Sylensky/OG-star-tracker-/community_upgrades/surveyor_tripod_adapter/size-test.stl

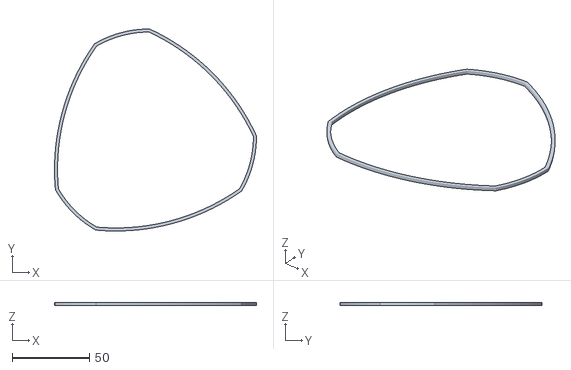
[picture p23: CAD file, 2025-09-13]
community_upgrades/surveyor_tripod_adapter/size-test.stl
130.6 x 130.6 x 2.00
