Sylensky/OG-star-tracker-/mechanics/Heavy duty/arcs-for-hd.stl

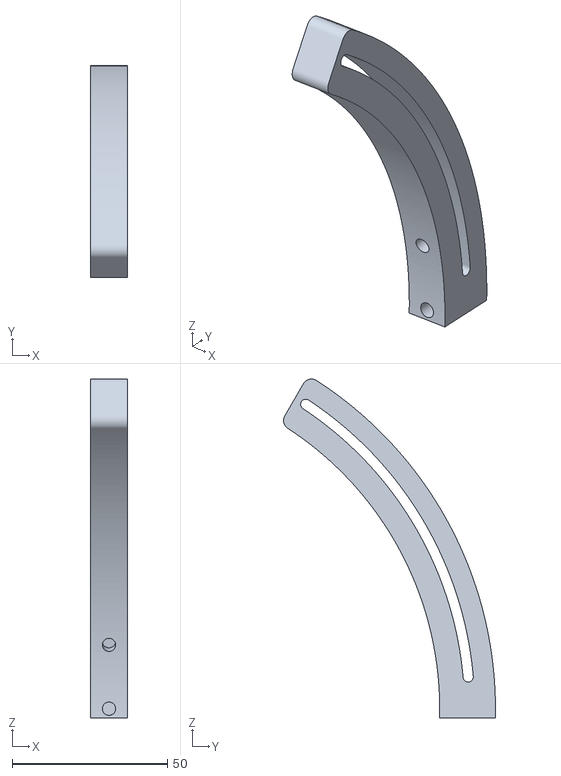
[picture p24: CAD file, 2025-09-13]
mechanics/Heavy duty/arcs-for-hd.stl
12.0 x 68.4 x 109.4
