Sylensky/OG-star-tracker-/mechanics/Manual go-to beta testing/vixen-knob.stl

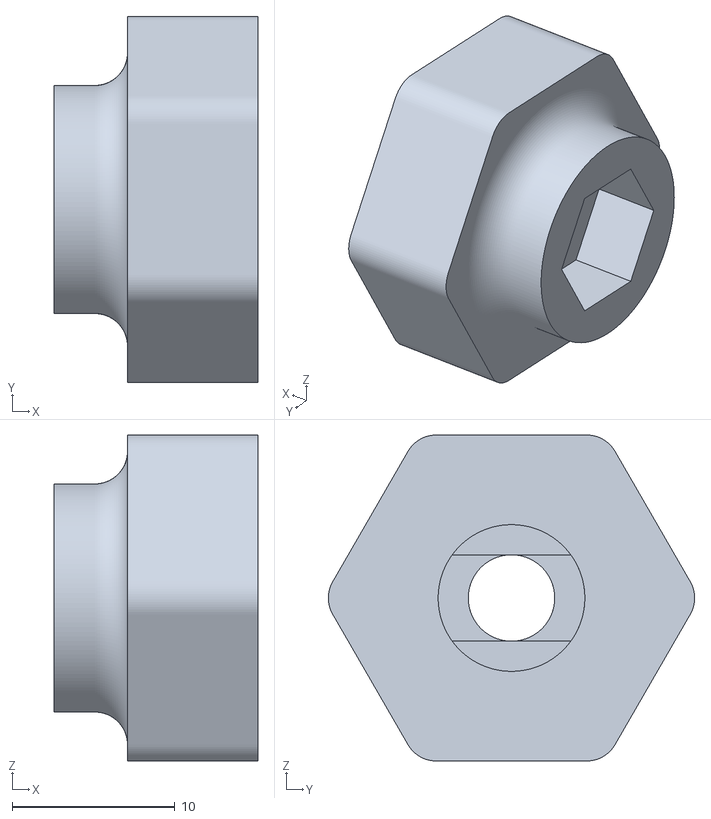
[picture p25: CAD file, 2025-09-13]
mechanics/Manual go-to beta testing/vixen-knob.stl
12.5 x 22.5 x 20.0
