Sylensky/OG-star-tracker-/mechanics/V2 files/polar-knob.stl

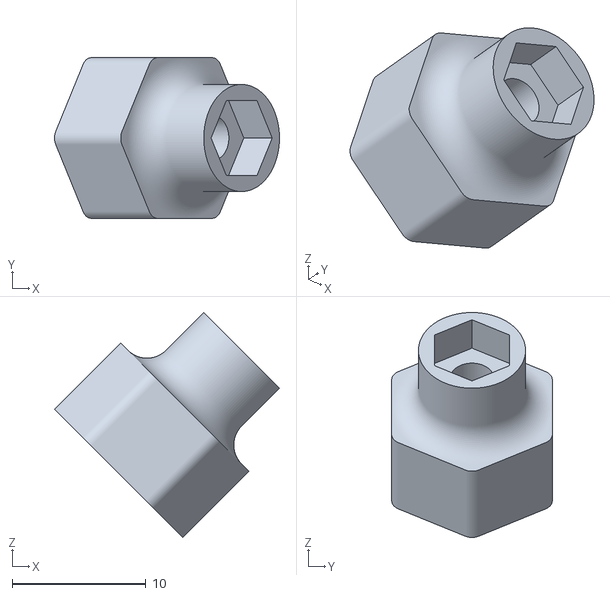
[picture p26: CAD file, 2025-09-13]
mechanics/V2 files/polar-knob.stl
16.8 x 12.0 x 16.8
