Sylensky/OG-star-tracker-/community_upgrades/beefier_gearbox_multicolor/stls/belt-tightener-f695-bearing-m5x16mm.stl

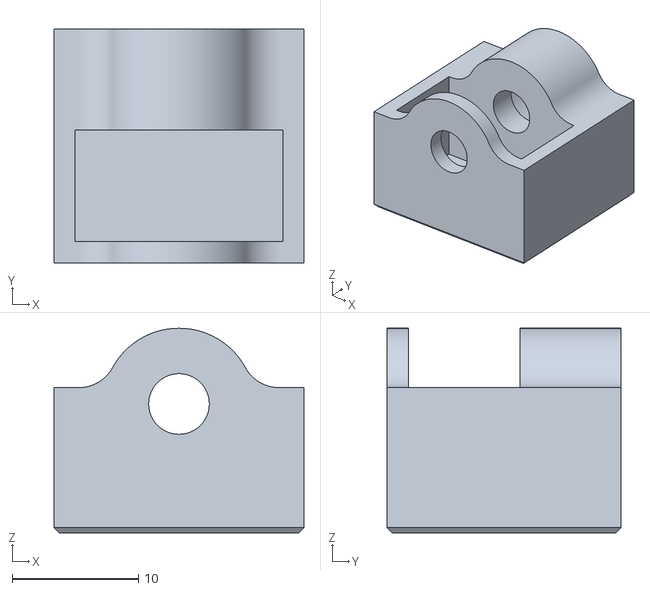
[picture p27: CAD file, 2025-09-13]
community_upgrades/beefier_gearbox_multicolor/stls/belt-tightener-f695-bearing-m5x16mm.stl
19.8 x 18.5 x 16.2
