Sylensky/OG-star-tracker-/community_upgrades/illuminated_polarscope/stls/scope-mount-body-pot-and-switch-v11.stl

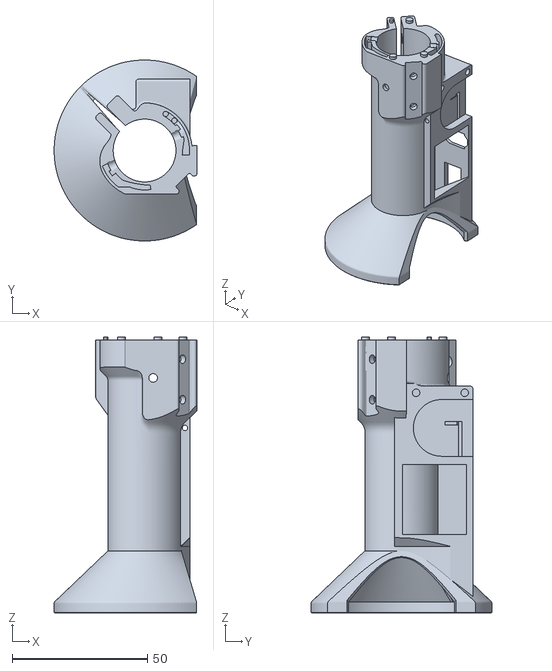
[picture p28: CAD file, 2025-10-03]
community_upgrades/illuminated_polarscope/stls/scope-mount-body-pot-and-switch-v11.stl
52.9 x 67.0 x 102.2
