Sylensky/OG-star-tracker-/mechanics/Manual go-to beta testing/big-scale.stl

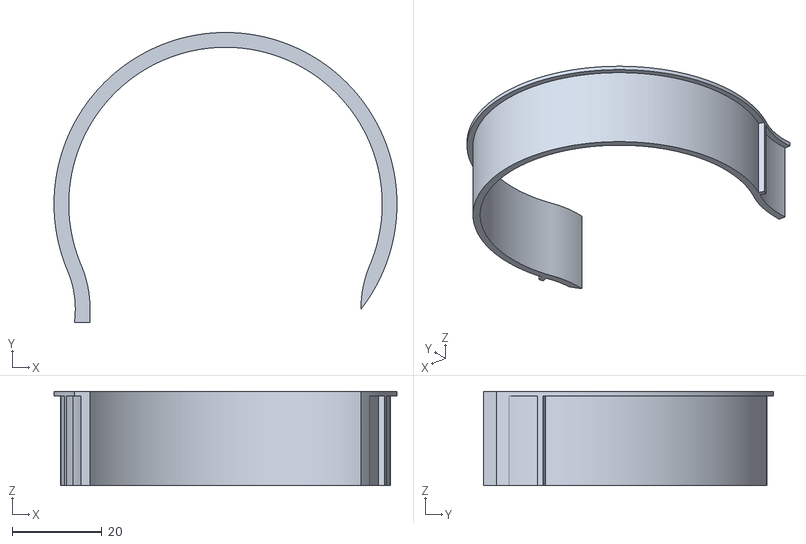
[picture p29: CAD file, 2025-09-13]
mechanics/Manual go-to beta testing/big-scale.stl
76.5 x 64.7 x 21.0
