Sylensky/OG-star-tracker-/mechanics/V2 files/bottom-bearing-holder.stl

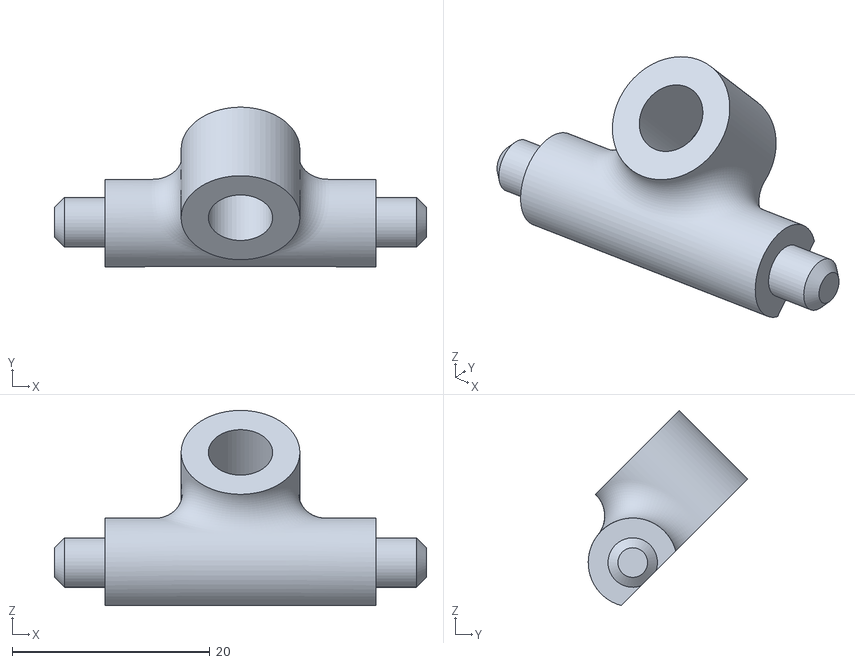
[picture p30: CAD file, 2025-09-13]
mechanics/V2 files/bottom-bearing-holder.stl
37.6 x 16.1 x 19.7
