Sylensky/OG-star-tracker-/community_upgrades/beefier_gearbox_multicolor/stls/belt-cover-modded-needs_supports.stl

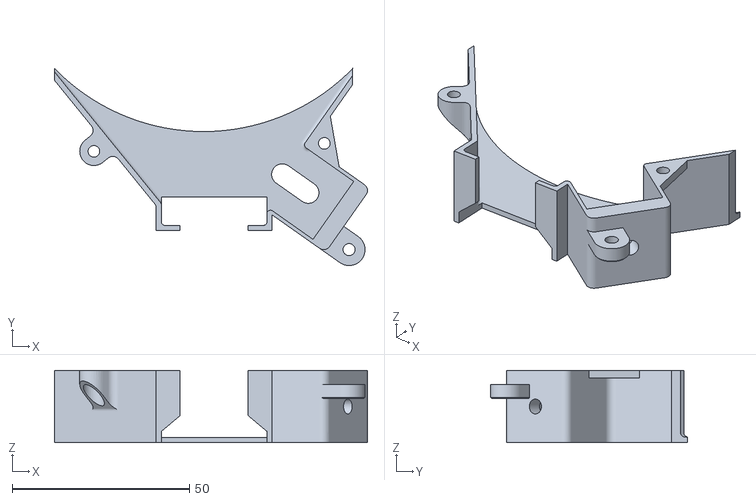
[picture p31: CAD file, 2025-09-13]
community_upgrades/beefier_gearbox_multicolor/stls/belt-cover-modded-needs_supports.stl
88.4 x 55.6 x 20.4
