Sylensky/OG-star-tracker-/community_upgrades/illuminated_polarscope/stls/potentiometer-hole-cover.stl

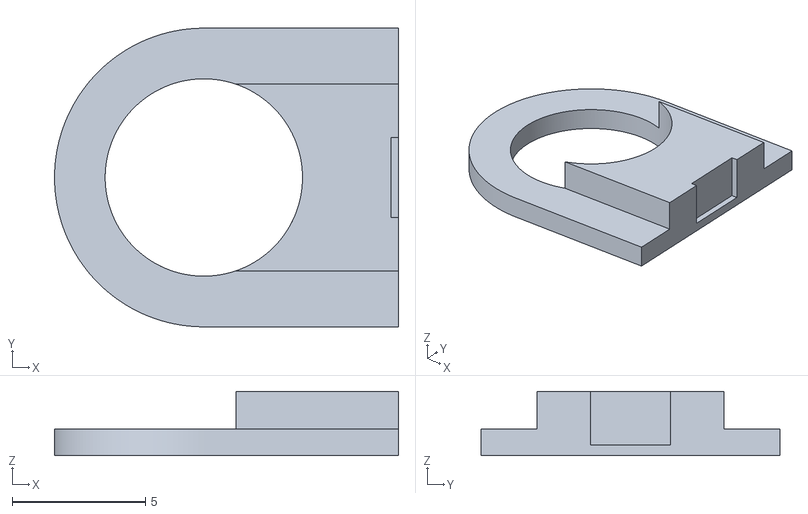
[picture p32: CAD file, 2025-10-03]
community_upgrades/illuminated_polarscope/stls/potentiometer-hole-cover.stl
12.9 x 11.2 x 2.40
