Sylensky/OG-star-tracker-/mechanics/Heavy duty/stationary-part-hd.stl

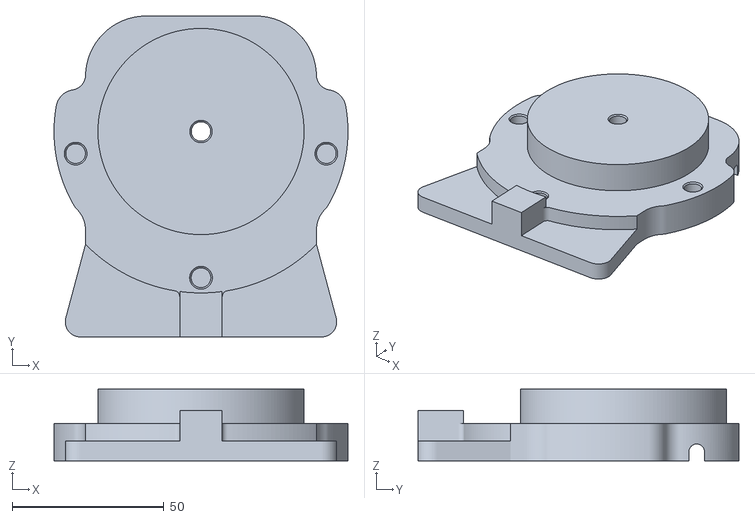
[picture p33: CAD file, 2025-09-13]
mechanics/Heavy duty/stationary-part-hd.stl
97.0 x 105.9 x 23.6
