Sylensky/OG-star-tracker-/mechanics/Manual go-to beta testing/vixen-holder.stl

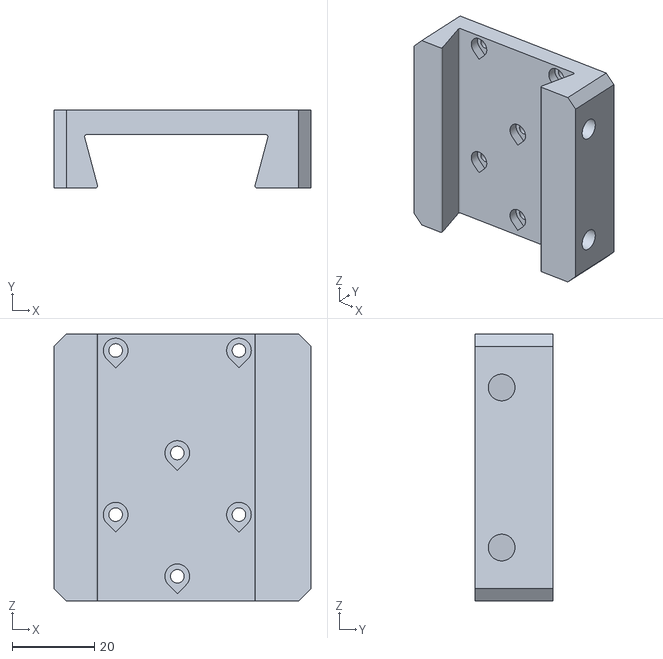
[picture p34: CAD file, 2025-09-13]
mechanics/Manual go-to beta testing/vixen-holder.stl
62.5 x 19.0 x 64.9
