Sylensky/OG-star-tracker-/mechanics/V2 files/tightener-bottom.stl

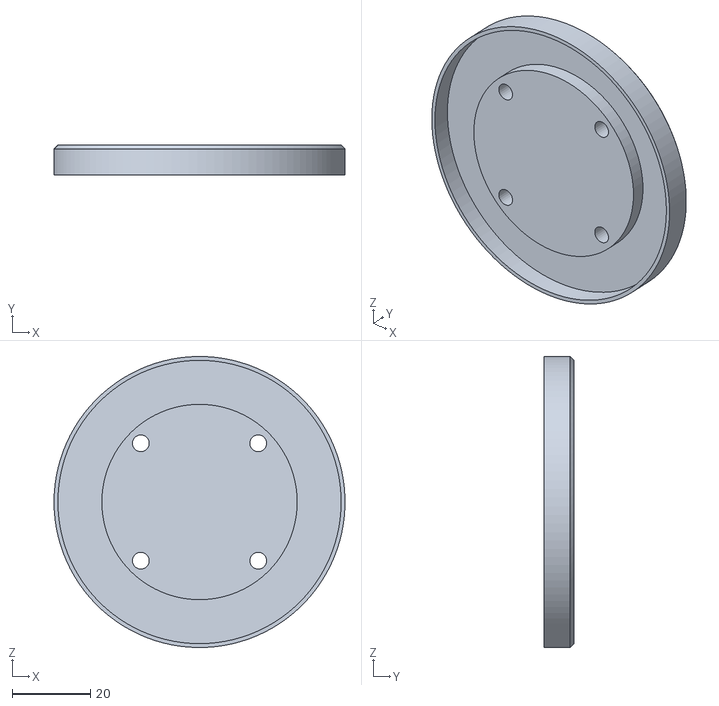
[picture p35: CAD file, 2025-09-13]
mechanics/V2 files/tightener-bottom.stl
74.5 x 7.70 x 74.5
