Sylensky/OG-star-tracker-/community_upgrades/beefier_gearbox_multicolor/stls/gearbox-part-1-2-combined-with-multicolor-letters-v11.stl

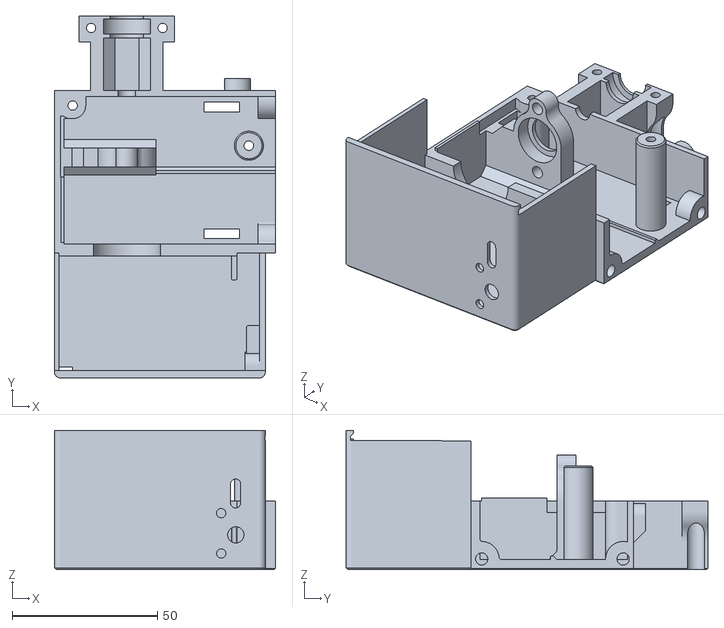
[picture p36: CAD file, 2025-09-13]
community_upgrades/beefier_gearbox_multicolor/stls/gearbox-part-1-2-combined-with-multicolor-letters-v11.stl
76.0 x 124.5 x 47.9
