Sylensky/OG-star-tracker-/community_upgrades/illuminated_polarscope/stls/knob.stl

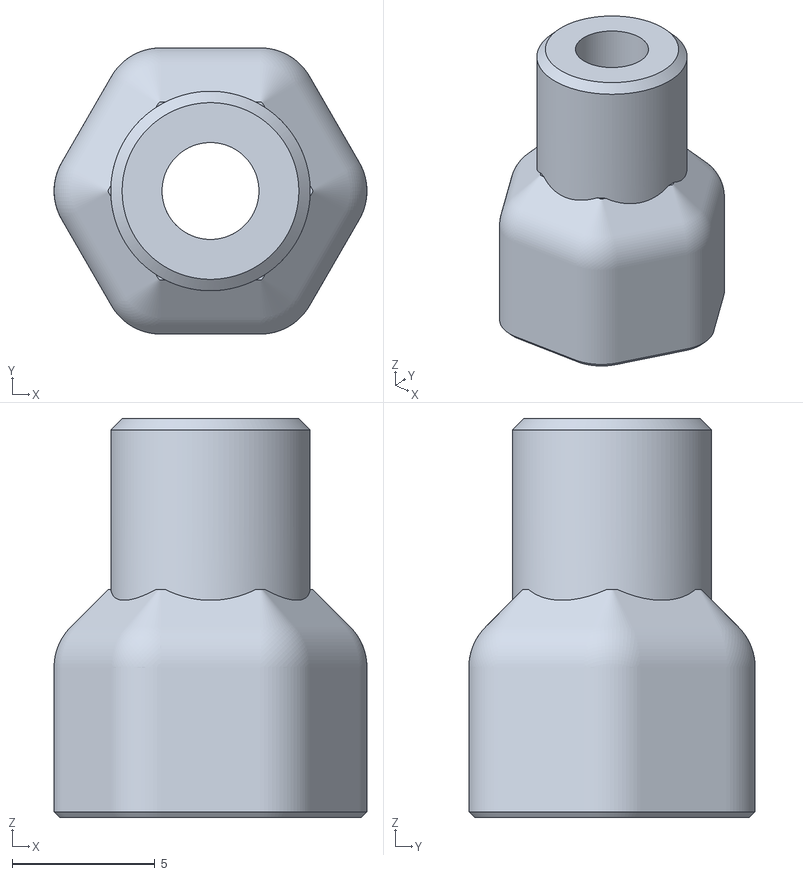
[picture p37: CAD file, 2025-10-03]
community_upgrades/illuminated_polarscope/stls/knob.stl
11.0 x 10.0 x 14.0
