Sylensky/OG-star-tracker-/mechanics/Manual go-to beta testing/small-scale-1.stl

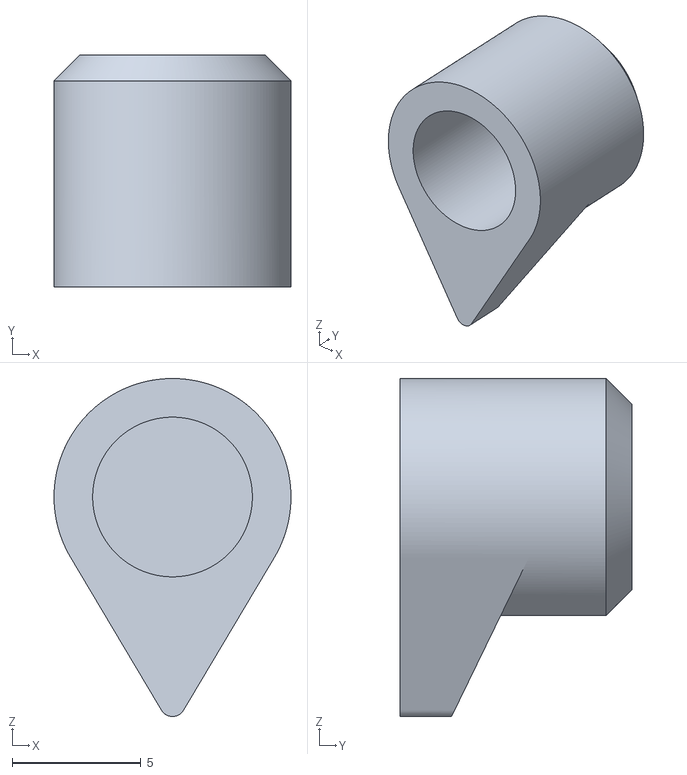
[picture p38: CAD file, 2025-09-13]
mechanics/Manual go-to beta testing/small-scale-1.stl
9.20 x 9.00 x 13.1
