Sylensky/OG-star-tracker-/mechanics/V2 files/gearbox-part-3.stl

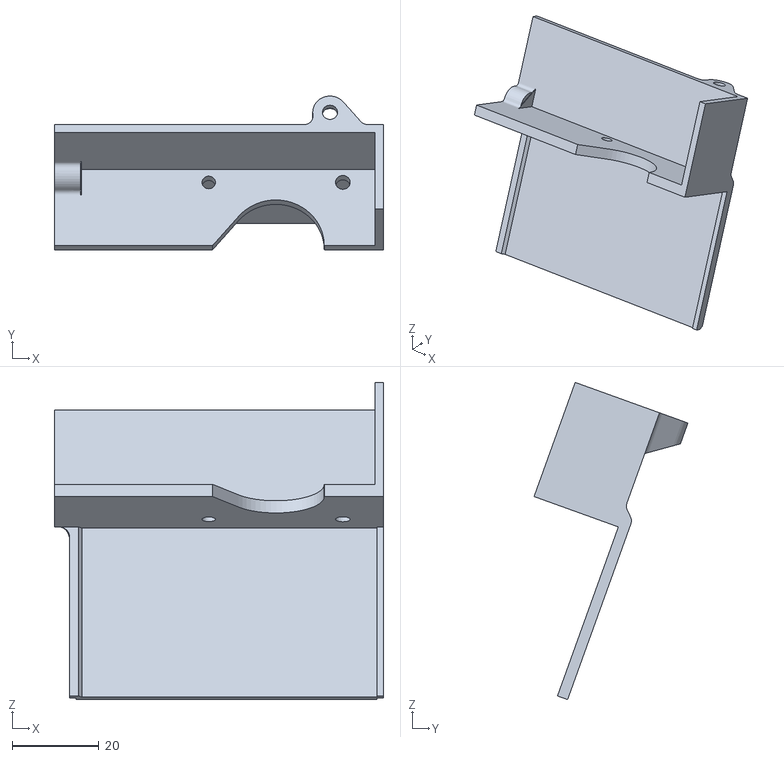
[picture p39: CAD file, 2025-09-13]
mechanics/V2 files/gearbox-part-3.stl
76.0 x 35.6 x 73.3
