Sylensky/OG-star-tracker-/community_upgrades/beefier_gearbox_multicolor/stls/gearbox-part-3-modded.stl

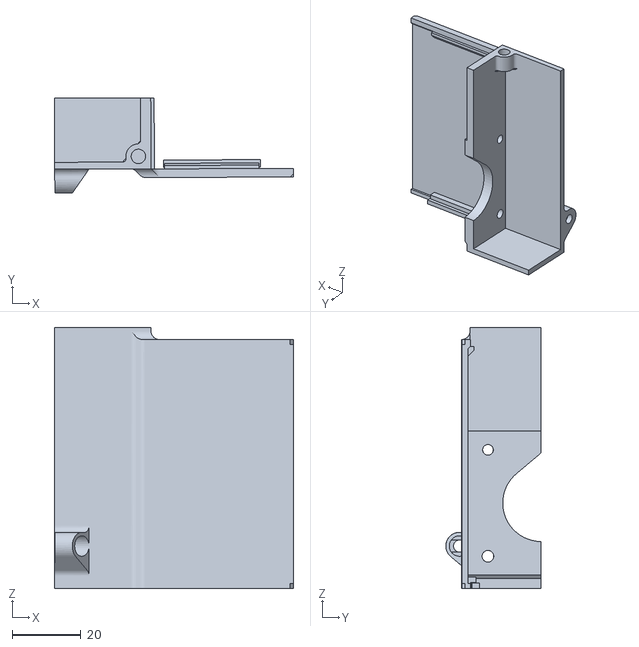
[picture p40: CAD file, 2025-09-13]
community_upgrades/beefier_gearbox_multicolor/stls/gearbox-part-3-modded.stl
69.6 x 27.8 x 76.0
