Sylensky/OG-star-tracker-/mechanics/V2 files/stationary-part-for-3-8-threaded-insert.stl

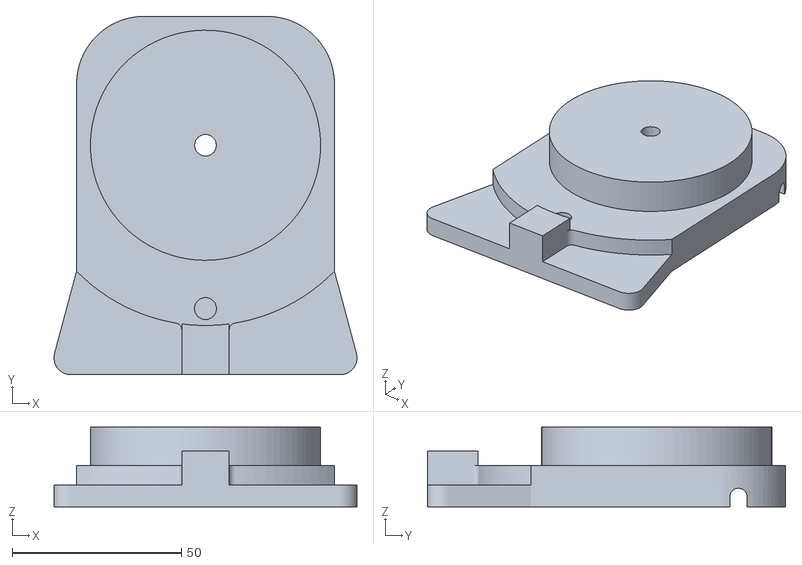
[picture p41: CAD file, 2025-09-13]
mechanics/V2 files/stationary-part-for-3-8-threaded-insert.stl
89.5 x 105.9 x 23.6
