Sylensky/OG-star-tracker-/community_upgrades/beefier_gearbox_multicolor/stls/doors-modded-with-logo.stl

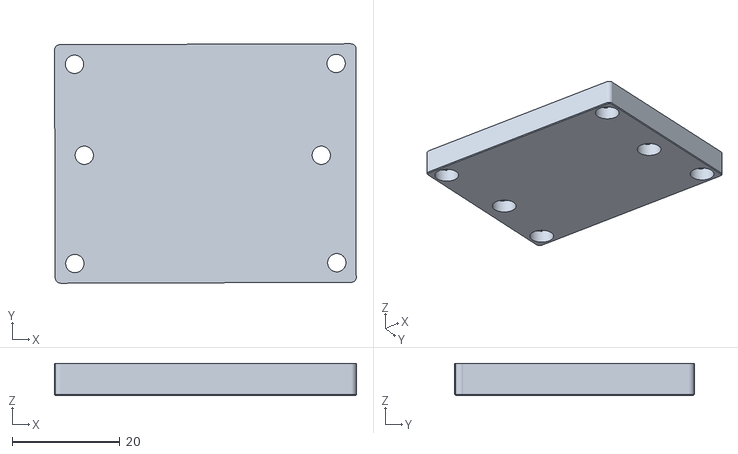
[picture p42: CAD file, 2025-09-13]
community_upgrades/beefier_gearbox_multicolor/stls/doors-modded-with-logo.stl
56.1 x 44.5 x 6.00
