Sylensky/OG-star-tracker-/mechanics/V2 files/belt-cover.stl

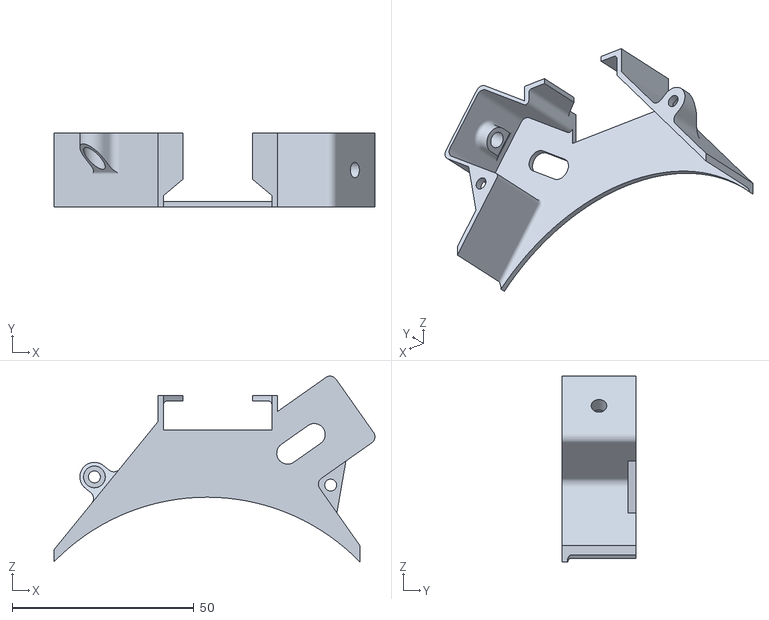
[picture p43: CAD file, 2025-09-13]
mechanics/V2 files/belt-cover.stl
88.4 x 20.4 x 51.2
