Sylensky/OG-star-tracker-/mechanics/V2 files/gearbox-part-4.stl

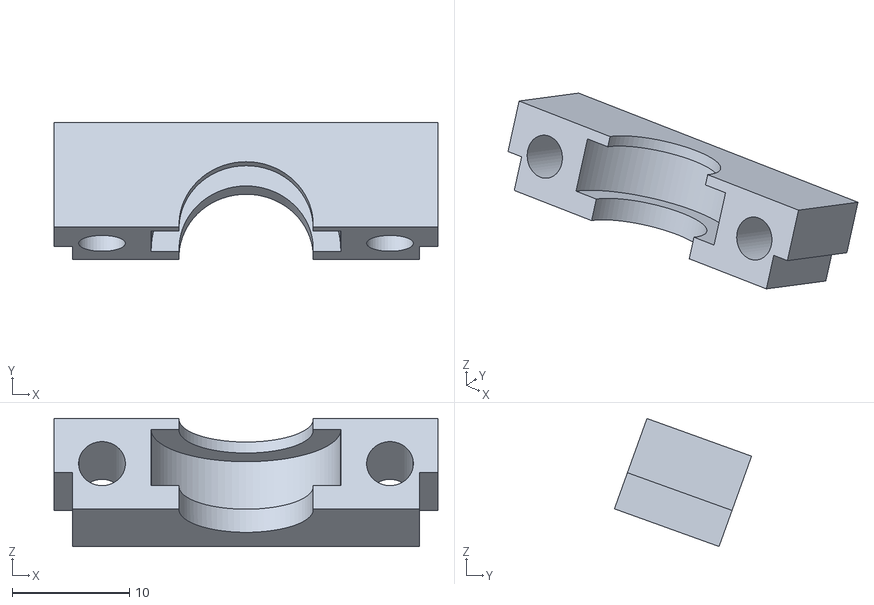
[picture p45: CAD file, 2025-09-13]
mechanics/V2 files/gearbox-part-4.stl
32.8 x 11.7 x 10.9
