Sylensky/OG-star-tracker-/mechanics/V2 files/side-m3-knob.stl

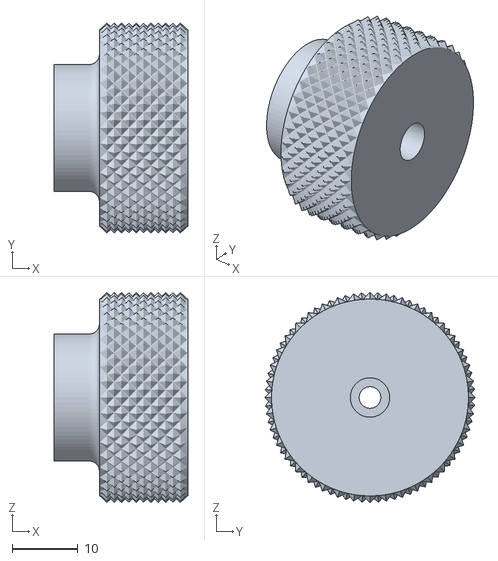
[picture p46: CAD file, 2025-09-13]
mechanics/V2 files/side-m3-knob.stl
20.4 x 32.0 x 32.0
