Sylensky/OG-star-tracker-/mechanics/V2 files/arc-left.stl

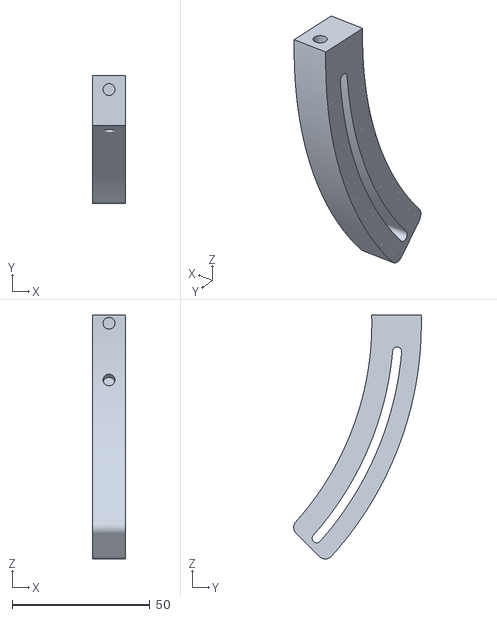
[picture p47: CAD file, 2025-09-13]
mechanics/V2 files/arc-left.stl
12.0 x 46.4 x 88.6
