Sylensky/OG-star-tracker-/mechanics/V2 files/belt-tightener.stl

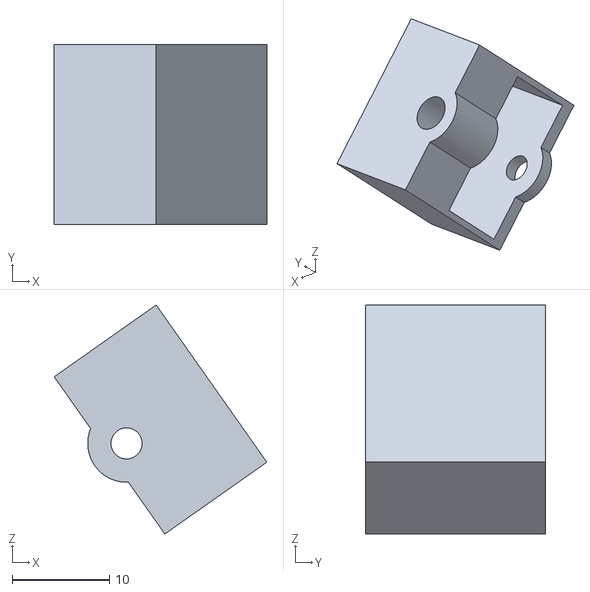
[picture p48: CAD file, 2025-09-13]
mechanics/V2 files/belt-tightener.stl
21.9 x 18.6 x 23.6
