Sylensky/OG-star-tracker-/mechanics/V2 files/bearing-holder.stl

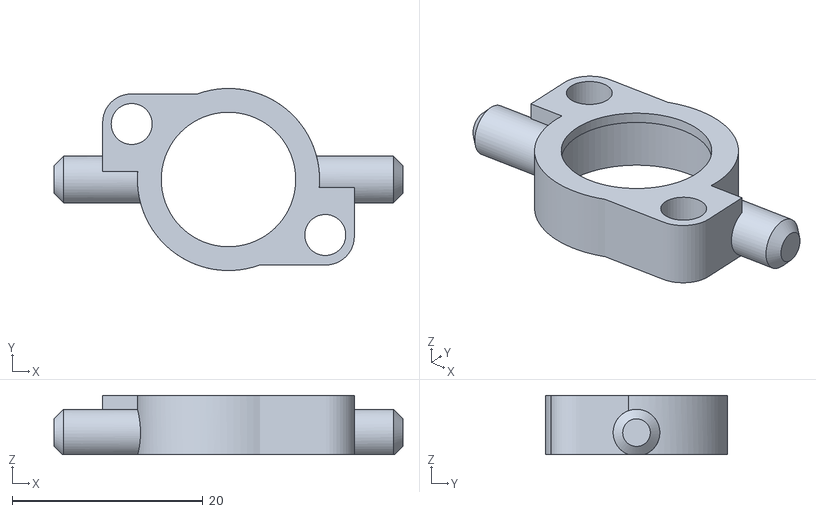
[picture p49: CAD file, 2025-09-13]
mechanics/V2 files/bearing-holder.stl
36.6 x 19.1 x 6.20
