Sylensky/OG-star-tracker-/mechanics/V2 files/m5-knob-small.stl

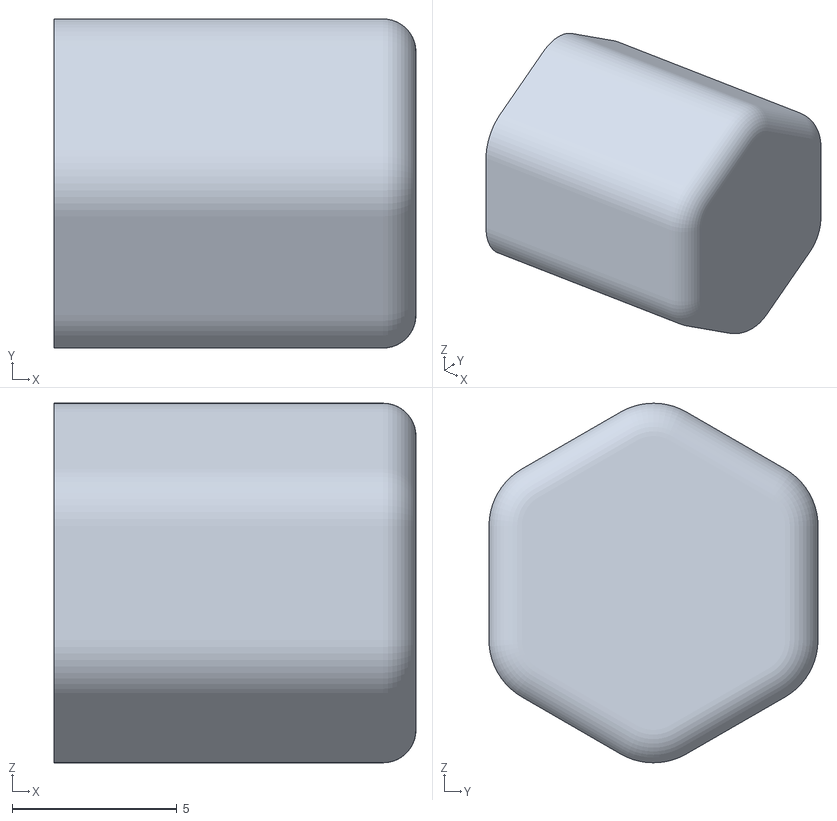
[picture p50: CAD file, 2025-09-13]
mechanics/V2 files/m5-knob-small.stl
11.0 x 10.0 x 10.9
