Sylensky/OG-star-tracker-/mechanics/V2 files/updated-tightener.stl

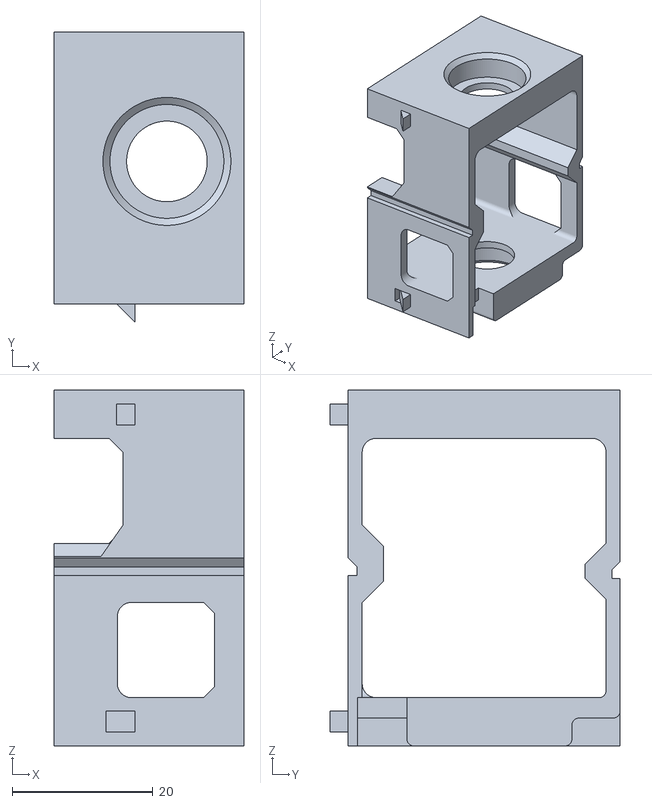
[picture p51: CAD file, 2025-09-13]
mechanics/V2 files/updated-tightener.stl
27.0 x 41.3 x 50.7
