Sylensky/OG-star-tracker-/mechanics/V2 files/laser-holder.stl

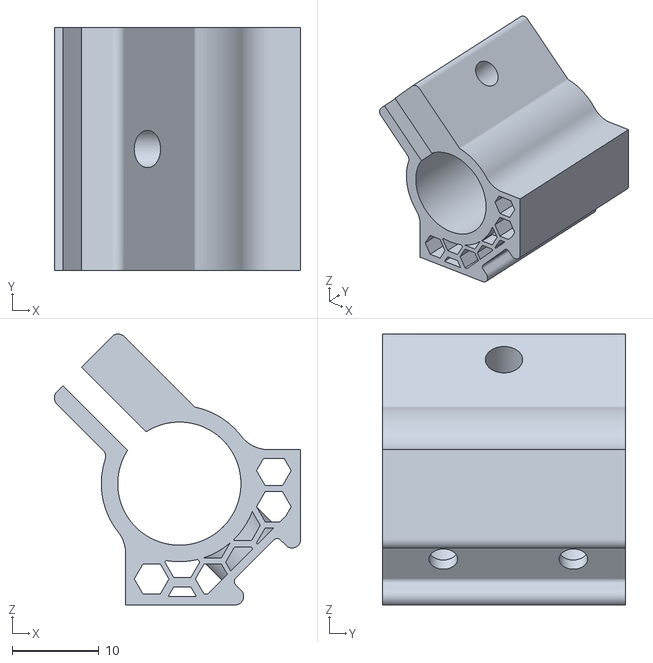
[picture p52: CAD file, 2025-09-13]
mechanics/V2 files/laser-holder.stl
28.4 x 28.0 x 31.3
