Sylensky/OG-star-tracker-/mechanics/V2 files/phone-holder.stl

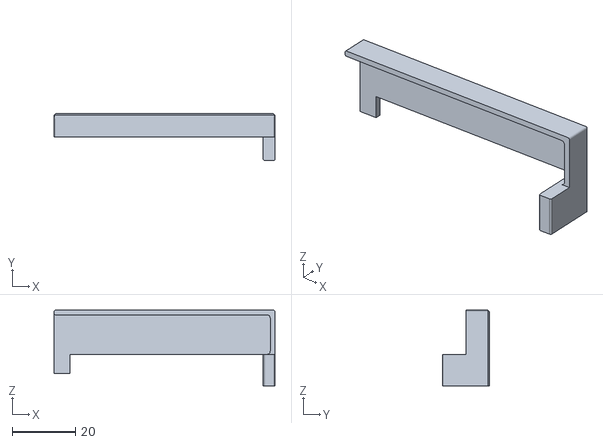
[picture p53: CAD file, 2025-09-13]
mechanics/V2 files/phone-holder.stl
69.9 x 14.9 x 24.0
