Sylensky/OG-star-tracker-/mechanics/V2 files/m5-knob-big.stl

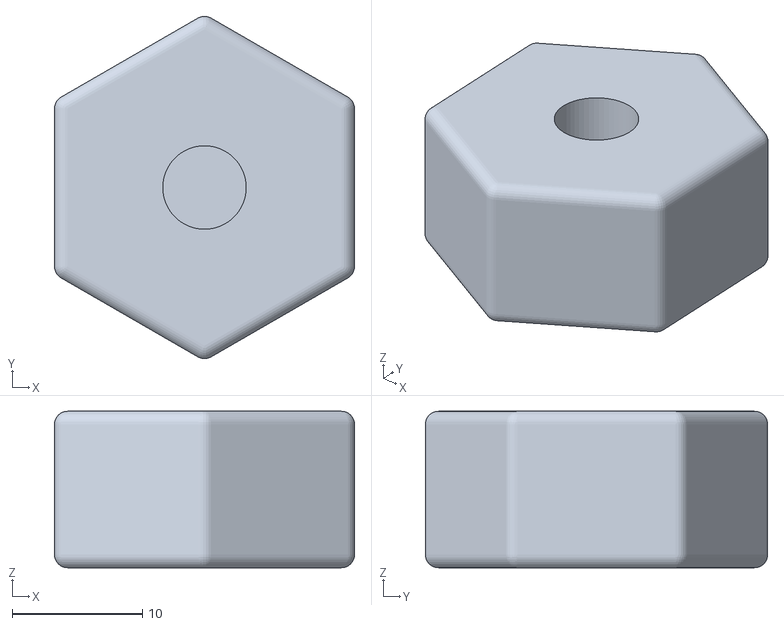
[picture p54: CAD file, 2025-09-13]
mechanics/V2 files/m5-knob-big.stl
23.0 x 26.2 x 12.0
