Sylensky/OG-star-tracker-/mechanics/V2 files/middle-holder.stl

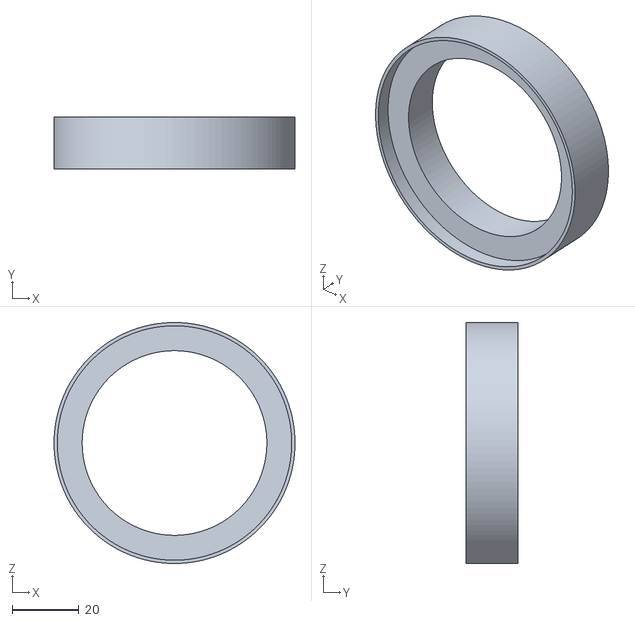
[picture p55: CAD file, 2025-09-13]
mechanics/V2 files/middle-holder.stl
72.3 x 15.5 x 72.3
