Sylensky/OG-star-tracker-/mechanics/V2 files/middle-holder-bottom.stl

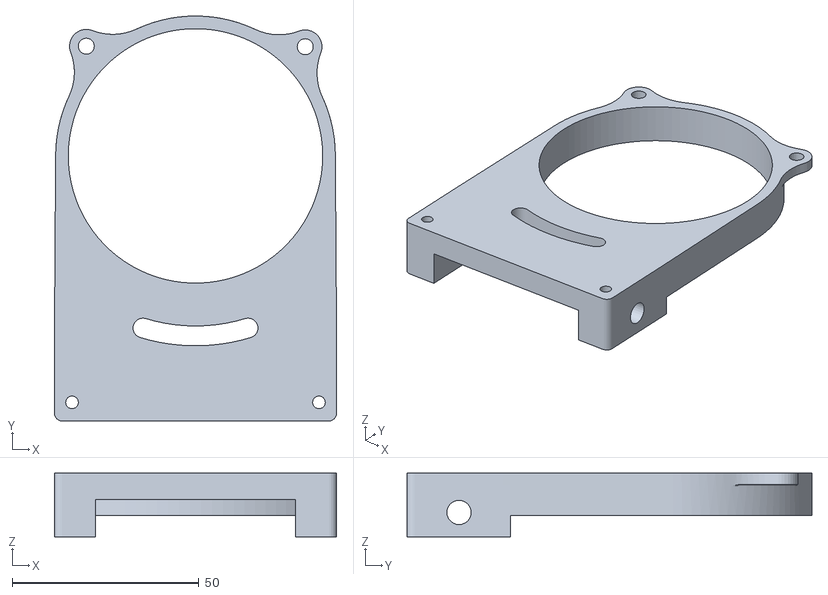
[picture p56: CAD file, 2025-09-13]
mechanics/V2 files/middle-holder-bottom.stl
75.6 x 108.6 x 17.1
