Sylensky/OG-star-tracker-/mechanics/V2 files/polar-scope-holder-eq5.stl

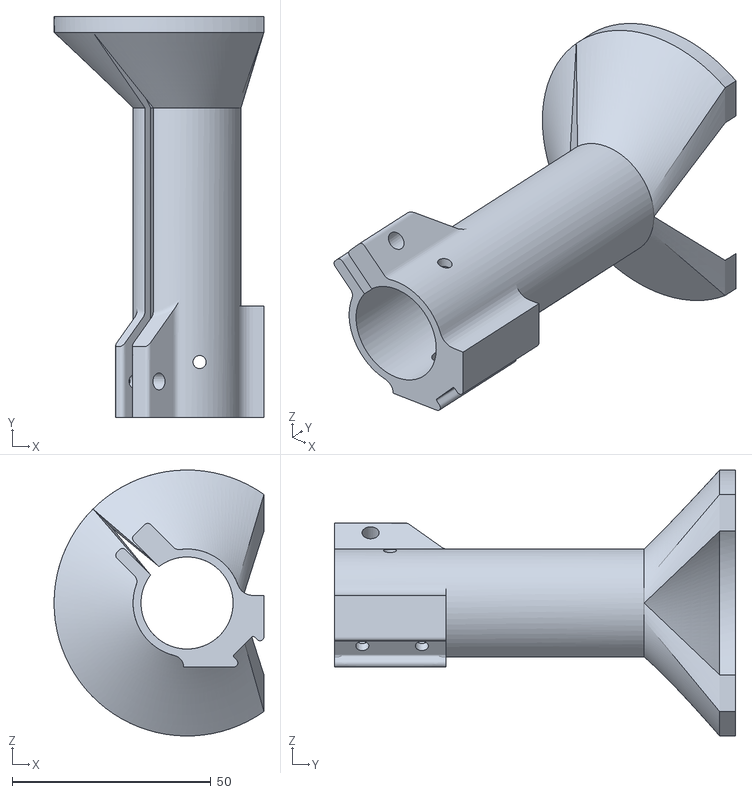
[picture p57: CAD file, 2025-09-13]
mechanics/V2 files/polar-scope-holder-eq5.stl
52.9 x 101.0 x 67.0
