Sylensky/OG-star-tracker-/mechanics/V2 files/rod-holder.stl

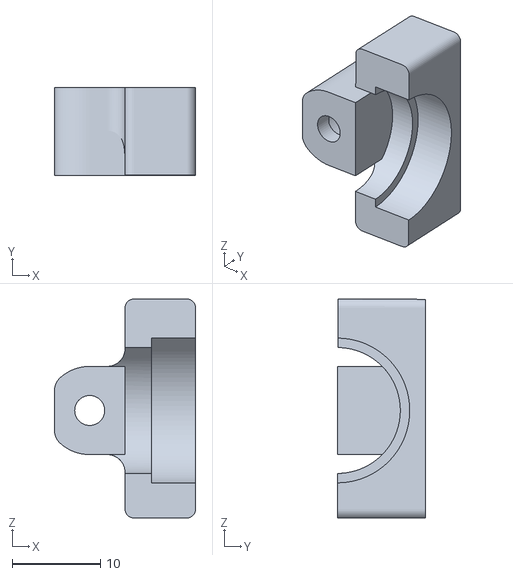
[picture p58: CAD file, 2025-09-13]
mechanics/V2 files/rod-holder.stl
16.0 x 10.0 x 24.8
