Sylensky/OG-star-tracker-/mechanics/V2 files/camera-holder.stl

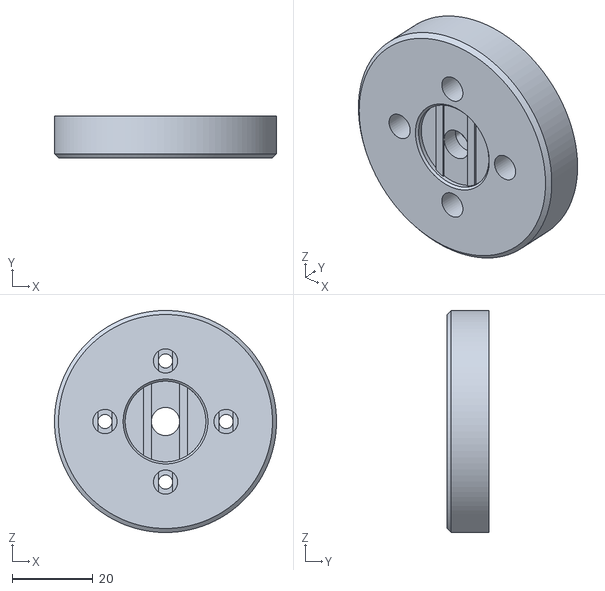
[picture p59: CAD file, 2025-09-13]
mechanics/V2 files/camera-holder.stl
55.0 x 10.4 x 55.0
