Sylensky/OG-star-tracker-/mechanics/V2 files/bearing-holder-cover.stl

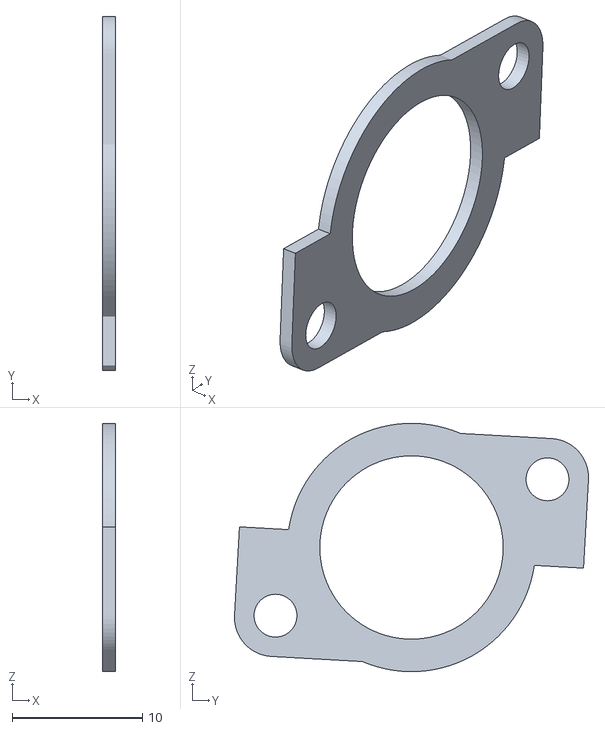
[picture p60: CAD file, 2025-09-13]
mechanics/V2 files/bearing-holder-cover.stl
1.00 x 27.2 x 19.1
