Sylensky/OG-star-tracker-/esp32_wireless_control/firmware/strings.cpp

#include "strings.h"
#include <WString.h>

// MIME type constants
const char *MIME_TYPE_TEXT = "text/plain";
const char *MIME_TYPE_HTML = "text/html";

// String lookup table structure
struct StringTable {
  const char *str;
  StringID id;
  Language lang;
};

// Parameter key lookup table structure
struct ParamKeyTable {
  const char *key;
  StringID id;
};

// Parameter key definitions
const ParamKeyTable paramKeys[] = {
    {.key = "trackingSpeed", .id = STR_TRACKING_SPEED},
    {.key = "speed", .id = STR_SPEED},
    {.key = "direction", .id = STR_DIRECTION},
    {.key = "exposure", .id = STR_EXPOSURE},
    {.key = "numExposures", .id = STR_NUM_EXPOSURES},
    {.key = "ditherEnabled", .id = STR_DITHER_ENABLED},
    {.key = "focalLength", .id = STR_FOCAL_LENGTH},
    {.key = "pixSize", .id = STR_PIXEL_SIZE},
    {.key = "disableTracking", .id = STR_DISABLE_TRACKING},
};

// All string definitions
const StringTable strings[] = {
    // English strings
    {.str = "Tracking ON", .id = STR_TRACKING_ON, .lang = EN},
    {.str = "Tracking OFF", .id = STR_TRACKING_OFF, .lang = EN},
    {.str = "Idle", .id = STR_IDLE, .lang = EN},
    {.str = "Slewing", .id = STR_SLEWING, .lang = EN},
    {.str = "Invalid Exposure Values!", .id = STR_INVALID_EXPOSURE, .lang = EN},
    {.str = "Invalid Dither Settings!", .id = STR_INVALID_DITHER, .lang = EN},
    {.str = "Capture Started", .id = STR_CAPTURE_ON, .lang = EN},
    {.str = "Capture Stopped", .id = STR_CAPTURE_OFF, .lang = EN},
    {.str = "Capture Already Running", .id = STR_CAPTURE_ALREADY_ON, .lang = EN},
    {.str = "Capture Already Stopped", .id = STR_CAPTURE_ALREADY_OFF, .lang = EN},
    {.str = "%d Captures Remaining...", .id = STR_CAPTURES_REMAINING, .lang = EN},

    // UI elements - English
    {.str = "OG Star Tracker Control Panel", .id = STR_TITLE, .lang = EN},
    {.str = "Tracking", .id = STR_TRACKING, .lang = EN},
    {.str = "Hemisphere", .id = STR_HEMISPHERE, .lang = EN},
    {.str = "North", .id = STR_NORTH, .lang = EN},
    {.str = "South", .id = STR_SOUTH, .lang = EN},
    {.str = "Tracking Rate", .id = STR_TRACKING_RATE, .lang = EN},
    {.str = "Sidereal", .id = STR_SIDEREAL, .lang = EN},
    {.str = "Solar", .id = STR_SOLAR, .lang = EN},
    {.str = "Lunar", .id = STR_LUNAR, .lang = EN},
    {.str = "Slew Control", .id = STR_SLEW_CONTROL, .lang = EN},
    {.str = "Speed Multiplier", .id = STR_SPEED_MULTIPLIER, .lang = EN},
    {.str = "Custom", .id = STR_CUSTOM, .lang = EN},
    {.str = "Custom Speed", .id = STR_CUSTOM_SPEED, .lang = EN},
    {.str = "Hold direction button to slew", .id = STR_SLEW_HINT, .lang = EN},
    {.str = "Slew Left", .id = STR_SLEW_LEFT, .lang = EN},
    {.str = "Slew Right", .id = STR_SLEW_RIGHT, .lang = EN},
    {.str = "Abort Slew", .id = STR_ABORT_SLEW, .lang = EN},
    {.str = "Photo Control", .id = STR_PHOTO_CONTROL, .lang = EN},
    {.str = "Exposure Length", .id = STR_EXPOSURE_LENGTH, .lang = EN},
    {.str = "in seconds (Ex. 30)", .id = STR_EXPOSURE_HINT, .lang = EN},
    {.str = "number of photos (Ex. 20)", .id = STR_NUM_EXPOSURES_HINT, .lang = EN},
    {.str = "Dither Settings", .id = STR_DITHER_SETTINGS, .lang = EN},
    {.str = "Enable Dithering", .id = STR_DITHER_ENABLE, .lang = EN},
    {.str = "in millimeters (Ex. 135)", .id = STR_FOCAL_LENGTH_HINT, .lang = EN},
    {.str = "in micrometers (Ex. 4.1)", .id = STR_PIXEL_SIZE_HINT, .lang = EN},
    {.str = "Start Capture", .id = STR_START_CAPTURE, .lang = EN},
    {.str = "Abort Capture", .id = STR_ABORT_CAPTURE, .lang = EN},
    {.str = "Status", .id = STR_STATUS, .lang = EN},
    {.str = "Ready", .id = STR_STATUS_MSG, .lang = EN},
    {.str = "Firmware Version", .id = STR_FIRMWARE_VERSION, .lang = EN},
    {.str = "ON", .id = STR_BTN_ON, .lang = EN},
    {.str = "OFF", .id = STR_BTN_OFF, .lang = EN},

    // Chinese strings
    {.str = "追踪开启", .id = STR_TRACKING_ON, .lang = CN},
    {.str = "追踪关闭", .id = STR_TRACKING_OFF, .lang = CN},
    {.str = "空闲", .id = STR_IDLE, .lang = CN},
    {.str = "快速调整中", .id = STR_SLEWING, .lang = CN},
    {.str = "无效的曝光参数!", .id = STR_INVALID_EXPOSURE, .lang = CN},
    {.str = "无效的抖动设置!", .id = STR_INVALID_DITHER, .lang = CN},
    {.str = "拍摄开始", .id = STR_CAPTURE_ON, .lang = CN},
    {.str = "拍摄停止", .id = STR_CAPTURE_OFF, .lang = CN},
    {.str = "拍摄已在进行中", .id = STR_CAPTURE_ALREADY_ON, .lang = CN},
    {.str = "拍摄已经停止", .id = STR_CAPTURE_ALREADY_OFF, .lang = CN},
    {.str = "剩余拍摄次数: %d", .id = STR_CAPTURES_REMAINING, .lang = CN},

    // UI elements - Chinese
    {.str = "OG 赤道仪控制面板", .id = STR_TITLE, .lang = CN},
    {.str = "追踪", .id = STR_TRACKING, .lang = CN},
    {.str = "半球", .id = STR_HEMISPHERE, .lang = CN},
    {.str = "北半球", .id = STR_NORTH, .lang = CN},
    {.str = "南半球", .id = STR_SOUTH, .lang = CN},
    {.str = "追踪速率", .id = STR_TRACKING_RATE, .lang = CN},
    {.str = "恒星速率", .id = STR_SIDEREAL, .lang = CN},
    {.str = "太阳速率", .id = STR_SOLAR, .lang = CN},
    {.str = "月球速率", .id = STR_LUNAR, .lang = CN},
    {.str = "快速调", .id = STR_SLEW_CONTROL, .lang = CN},
    {.str = "速度倍率", .id = STR_SPEED_MULTIPLIER, .lang = CN},
    {.str = "自定义", .id = STR_CUSTOM, .lang = CN},
    {.str = "自定义速度", .id = STR_CUSTOM_SPEED, .lang = CN},
    {.str = "按住方向按钮进行快速调整", .id = STR_SLEW_HINT, .lang = CN},
    {.str = "向左调整", .id = STR_SLEW_LEFT, .lang = CN},
    {.str = "向右调整", .id = STR_SLEW_RIGHT, .lang = CN},
    {.str = "停止调整", .id = STR_ABORT_SLEW, .lang = CN},
    {.str = "拍摄控制", .id = STR_PHOTO_CONTROL, .lang = CN},
    {.str = "曝光时长", .id = STR_EXPOSURE_LENGTH, .lang = CN},
    {.str = "单位：秒 (例如: 30)", .id = STR_EXPOSURE_HINT, .lang = CN},
    {.str = "拍摄张数 (例如: 20)", .id = STR_NUM_EXPOSURES_HINT, .lang = CN},
    {.str = "抖动设置", .id = STR_DITHER_SETTINGS, .lang = CN},
    {.str = "启用抖动", .id = STR_DITHER_ENABLE, .lang = CN},
    {.str = "单位：毫米 (例如: 135)", .id = STR_FOCAL_LENGTH_HINT, .lang = CN},
    {.str = "单位：微米 (例如: 4.1)", .id = STR_PIXEL_SIZE_HINT, .lang = CN},
    {.str = "开始拍摄", .id = STR_START_CAPTURE, .lang = CN},
    {.str = "停止拍摄", .id = STR_ABORT_CAPTURE, .lang = CN},
    {.str = "状态", .id = STR_STATUS, .lang = CN},
    {.str = "就绪", .id = STR_STATUS_MSG, .lang = CN},
    {.str = "固件版本", .id = STR_FIRMWARE_VERSION, .lang = CN},
    {.str = "开启", .id = STR_BTN_ON, .lang = CN},
    {.str = "关闭", .id = STR_BTN_OFF, .lang = CN},
    {.str = "中文", .id = STR_LANG_CN, .lang = EN},
    {.str = "中文", .id = STR_LANG_CN, .lang = CN},
};

// Function to get a string
const char *getString(StringID id, Language lang) {
  // Iterate through the lookup table to find the matching string
  for (const auto &entry : strings) {
    if (entry.id == id && entry.lang == lang) {
      return entry.str;
    }
  }
  // If the requested language version is not found, return the English version
  if (lang != EN) {
    return getString(id, EN);
  }
  return ""; // If nothing is found, return an empty string
}

// Function to get the parameter key name
const char *getParamKey(StringID id) {
  for (const auto &entry : paramKeys) {
    if (entry.id == id) {
      return entry.key;
    }
  }
  return "";
}

const char *LOGO_BASE64 = "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";

const char *html_template = R"rawliteral(
<!DOCTYPE html>
<html>
<head>
    <meta charset='utf-8'>
    <meta name='viewport' content='width=device-width, initial-scale=1.0'>
    <title>%TITLE%</title>
    <style>
        body {
            background-color: #000000;
            text-align: center;
            font-family: system-ui;
            display: flex;
            padding: 10px;
            justify-content: center;
        }
        button {
            background-color: #FF0000;
            color: black;
            border: none;
            padding: 10px 10px;
            border-radius: 40px;
            text-align: center;
            text-decoration: none;
            display: inline-block;
            font-size: 14px;
            font-family: system-ui;
            margin-top: 10px;
            cursor: pointer;
            width: 50%;
            min-width: 120px;
            font-weight: bold;
        }
        select {
            font-size: 16px;
            padding: 5px;
            color: red;
            background-color: #000000;
            border: 2px solid #ff0000;
            border-radius: 8px;
            font-family: system-ui;
        }
        input[type='number'] {
            font-size: 16px;
            background-color: #000000;
            padding: 5px;
            font-family: system-ui;
            border: 2px solid #ff0000;
            color: red;
            border-radius: 8px;
            box-sizing: border-box;
        }
        label {
            display: inline-block;
            text-align: left;
            margin: 10px;
            font-size: 20px;
        }
        h1 {
            font-size: 26px;
            font-family: system-ui;
            color: red;
        }
        h2 {
            font-size: 24px;
            font-family: system-ui;
            color: red;
        }
        h3 {
            font-size: 16px;
            font-family: system-ui;
            color: #FF6B00;
        }
        h4 {
            font-size: 12px;
            font-family: system-ui;
            color: #FF6B00;
        }
        summary {
            font-weight: bold;
            font-family: system-ui;
            font-size: 16px;
            padding-top: 20px;
            color: #FF6B00;
        }
        .content {
            max-width: 450px;
            width: 100%;
            background-color: #000000;
        }
        .card {
            background-color: #000000;
            padding: 1px 16px 16px 16px;
            border-radius: 32px;
            margin-top: 20px;
            box-shadow: 0em 0em 1em rgb(255 0 0 / 100%);
        }
        .grid2 {
            display: flex;
            flex-direction: row;
            flex-wrap: wrap;
            color: #FF6B00;
            justify-content: center;
            align-items: center;
        }
        .grid2 > h3 {
            width: 50%;
            min-width: 120px;
        }
        .grid2 > select,
        .grid2 > input {
            width: 50%;
            min-width: 120px;
            height: 40px;
        }
        .grid2 > .checkbox {
            width: 50%;
            min-width: 120px;
            height: 20px;
            margin: 0px;
        }
        .header {
            display: flex;
            justify-content: center;
        }
        #logo {
            background-image: url('data:image/png;base64,%LOGO%');
            width: 150px;
            height: 120px;
            margin-top: 10px;
        }
        .button-group {
            padding-top: 10px;
            display: flex;
            flex-wrap: wrap;
            justify-content: center;
        }
        .right-separator {
            border-right: 2px solid #000000;
            -webkit-user-select: none;
            -moz-user-select: none;
            -ms-user-select: none;
            user-select: none;
            -webkit-touch-callout: none;
        }
        .left-separator {
            border-left: 2px solid #000000;
            -webkit-user-select: none;
            -moz-user-select: none;
            -ms-user-select: none;
            user-select: none;
            -webkit-touch-callout: none;
        }
        #status {
            font-size: 24px;
            margin: 0px;
            font-family: system-ui;
        }
    </style>
    <script>
        var lastClick = 0;
        var delay = 500;
        
        function sendRequest(url) {
            var xhr = new XMLHttpRequest();
            xhr.onreadystatechange = function() {
                if (this.readyState == 4 && this.status == 200) {
                    document.getElementById('status').innerHTML = this.responseText;
                }
            };
            xhr.open('GET', url, true);
            xhr.send();
        }

        setInterval(function() {
            sendRequest('/status');
        }, 5000);

        function requestFirmwareVersion() {
            var xhr = new XMLHttpRequest();
            xhr.onreadystatechange = function() {
                if (this.readyState == 4 && this.status == 200) {
                    document.getElementById('firmware').innerHTML = '%FIRMWARE_VERSION%: ' + this.responseText;
                }
            };
            xhr.open('GET', '/version', true);
            xhr.send();
        }

        function sendStartRequest(url) {
            var direction = document.getElementById('hemisphere-select').value;
            var trackingSpeed = document.getElementById('tracking-speed-select').value;
            var starturl = url + '?direction=' + direction + '&trackingSpeed=' + trackingSpeed;
            sendRequest(starturl);
        }

        function sendSlewStop() {
            lastClick = Date.now();
            sendRequest('/stopslew');
        }

        function sendSlewRequest(url) {
            if (lastClick >= (Date.now() - delay))
                return;
            lastClick = Date.now();
            var index = document.getElementById('slew-select').selectedIndex;
            if (index == 6) {
                var speed = document.getElementById('custom-speed').value;
            } else {
                var speed = document.getElementById('slew-select').value;
            }
            var slewurl = url + '?speed=' + speed;
            sendRequest(slewurl);
        }

        function checkCustom() {
            var index = document.getElementById('slew-select').selectedIndex;
            if (index == 6) {
                document.getElementById('custom-speed-text').style.display='block';
                document.getElementById('custom-speed').style.display='block';
            } else {
                document.getElementById('custom-speed-text').style.display='none';
                document.getElementById('custom-speed').style.display='none';
            }
        }

        function sendCaptureRequest() {
            var exposure = document.getElementById('exposure').value.trim();
            var numExposures = document.getElementById('num-exposures').value.trim();
            var focalLength = document.getElementById('focal_len').value.trim();
            var pixSize = Math.floor(parseFloat(document.getElementById('pixel_size').value.trim()) * 100);
            var disableTracking = document.getElementById('Disable_tracking_End').checked ? 1 : 0;
            var ditherEnabled = document.getElementById('dither_on').checked ? 1 : 0;
            var intervalometerUrl = '/start?exposure=' + exposure + 
                                  '&numExposures=' + numExposures + 
                                  '&focalLength=' + focalLength + 
                                  '&pixSize=' + pixSize + 
                                  '&ditherEnabled=' + ditherEnabled +
                                  '&disableTracking=' + disableTracking;
            sendRequest(intervalometerUrl);
        }

        function changeLanguage() {
            var lang = document.getElementById('language-select').value;
            var xhr = new XMLHttpRequest();
            xhr.onreadystatechange = function() {
                if (this.readyState == 4 && this.status == 200) {
                    window.location.reload(); // 强制刷新页面
                }
            };
            xhr.open('GET', '/setlang?lang=' + lang, true);
            xhr.send();
        }
    </script>
</head>
<body onload="requestFirmwareVersion()">
    <div class="content">
        <div class="language-selector">
            <select id="language-select" onchange="changeLanguage()">
                <option value="en" %lang_en%>English</option>
                <option value="cn" %lang_cn%>%LANG_CN%</option>
            </select>
        </div>
        <div class="header">
            <div id="logo"></div>
        </div>
        <h1>%TITLE%</h1>
        
        <div class="card">
            <h2>%TRACKING%</h2>
            <div class="grid2">
                <h3>%HEMISPHERE%</h3>
                <select id="hemisphere-select">
                    <option value="1" %north%>%NORTH%</option>
                    <option value="0" %south%>%SOUTH%</option>
                </select>
            </div>
            <div class="grid2">
                <h3>%TRACKING_RATE%</h3>
                <select id="tracking-speed-select">
                    <option value="0">%SIDEREAL%</option>
                    <option value="1">%SOLAR%</option>
                    <option value="2">%LUNAR%</option>
                </select>
            </div>
            <div class="button-group">
                <button class="right-separator" onclick="sendStartRequest('/on')">%BTN_ON%</button>
                <button class="left-separator" onclick="sendRequest('/off')">%BTN_OFF%</button>
            </div>
        </div>

        <div class="card">
            <h2>%SLEW_CONTROL%</h2>
            <div class="grid2">
                <h3>%SPEED_MULTIPLIER%</h3>
                <select id="slew-select" onchange="checkCustom()">
                    <option value="2">2 x %TRACKING_RATE%</option>
                    <option value="8">8</option>
                    <option value="50">50</option>
                    <option value="100">100</option>
                    <option value="200">200</option>
                    <option value="400">400</option>
                    <option value="custom">%CUSTOM%</option>
                </select>
            </div>
            <div class="grid2">
                <h3 id="custom-speed-text" style="display:none">%CUSTOM_SPEED%</h3>
                <input id="custom-speed" type="number" value="2" min="2" max="400" style="display:none"/>
            </div>
            <h4>%SLEW_HINT%</h4>
            <div class="button-group">
                <button class="right-separator" ontouchstart="sendSlewRequest('/left')" 
                        onmousedown="sendSlewRequest('/left')" 
                        ontouchend="sendSlewStop()" 
                        onmouseup="sendSlewStop()" 
                        onmouseleave="sendSlewStop()" 
                        ontouchcancel="sendSlewStop()">%SLEW_LEFT%</button>
                <button class="left-separator" ontouchstart="sendSlewRequest('/right')" 
                        onmousedown="sendSlewRequest('/right')" 
                        ontouchend="sendSlewStop()" 
                        onmouseup="sendSlewStop()" 
                        onmouseleave="sendSlewStop()" 
                        ontouchcancel="sendSlewStop()">%SLEW_RIGHT%</button>
            </div>
            <button onclick="sendSlewStop()">%ABORT_SLEW%</button>
        </div>

        <div class="card">
            <h2>%PHOTO_CONTROL%</h2>
            <div class="grid2">
                <h3>%EXPOSURE_LENGTH%</h3>
                <input type="number" id="exposure" placeholder="%EXPOSURE_HINT%">
            </div>
            <div class="grid2">
                <h3>%NUM_EXPOSURES%</h3>
                <input type="number" id="num-exposures" placeholder="%NUM_EXPOSURES_HINT%">
            </div>
            <div class="grid2">
                <h3>%DISABLE_TRACKING%</h3>
                <input class="checkbox" type="checkbox" id="Disable_tracking_End" %tracking%>
            </div>
            <details>
                <summary>%DITHER_SETTINGS%</summary>
                <div class="grid2">
                    <h3>%DITHER_ENABLE%</h3>
                    <input class="checkbox" type="checkbox" id="dither_on" %dither%>
                </div>
                <div class="grid2">
                    <h3>%FOCAL_LENGTH%</h3>
                    <input type="number" id="focal_len" placeholder="%FOCAL_LENGTH_HINT%" value="%focallen%">
                </div>
                <div class="grid2">
                    <h3>%PIXEL_SIZE%</h3>
                    <input type="number" id="pixel_size" placeholder="%PIXEL_SIZE_HINT%" value="%pixsize%" step="0.01">
                </div>
            </details>
            <div class="button-group">
                <button class="right-separator" onclick="sendCaptureRequest()">%START_CAPTURE%</button>
                <button class="left-separator" onclick="sendRequest('/abort')">%ABORT_CAPTURE%</button>
            </div>
        </div>

        <div class="card">
            <h2>%STATUS%</h2>
            <h3 id="status">%STATUS_MSG%</h3>
        </div>
        <h4 id="firmware">%FIRMWARE_VERSION%: </h4>
    </div>
</body>
</html>
)rawliteral";

String getHTML() {
  return String(html_template);
}
